22yeets22/Adjustable-Power-Supply/Wiring Diagram.kicad_sch

## KiCad design Wiring Diagram.kicad_sch (2026-02-19)

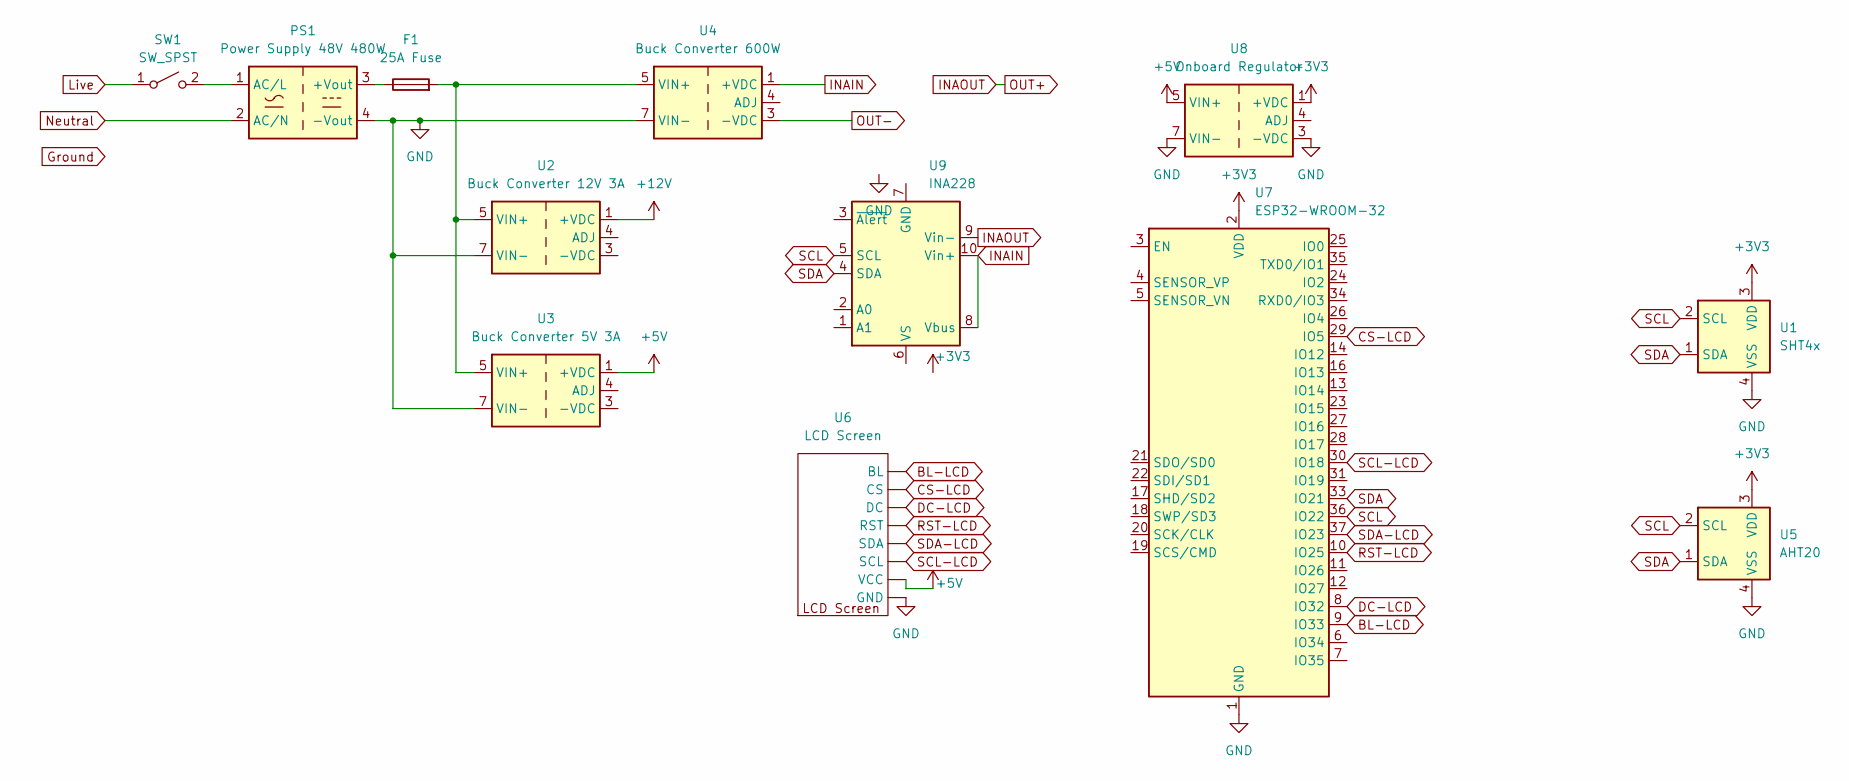
[picture p10: schematic Wiring Diagram.kicad_sch]

Parts:
F1: 25A Fuse
PS1: Power Supply 48V 480W; Converter_ACDC_MeanWell_IRM-60-xx_THT
SW1: SW_SPST
U1: SHT4x; Sensirion_DFN-4_1.5x1.5mm_P0.8mm_SHT4x_NoCentralPad
U2: Buck Converter 12V 3A; Converter_DCDC_Silvertel_Ag99xxLP_THT
U3: Buck Converter 5V 3A; Converter_DCDC_Silvertel_Ag99xxLP_THT
U4: Buck Converter 600W; Converter_DCDC_Silvertel_Ag99xxLP_THT
U5: AHT20; Sensirion_DFN-4_1.5x1.5mm_P0.8mm_SHT4x_NoCentralPad
U6: LCD Screen
U7: ESP32-WROOM-32
U8: Onboard Regulator; Converter_DCDC_Silvertel_Ag99xxLP_THT
U9: INA228; VSSOP-10_3x3mm_P0.5mm

Connections:
+3V3: U1.3 (VDD), U5.3 (VDD), U7.2 (VDD), U8.1 (+VDC), U8.2 (+VDC)
+5V: U3.1 (+VDC), U3.2 (+VDC), U6., U8.5 (VIN+), U8.6 (VIN+)
+12V: U2.1 (+VDC), U2.2 (+VDC)
BL-LCD: U6., U7.9 (IO33)
CS-LCD: U6., U7.29 (IO5)
DC-LCD: U6., U7.8 (IO32)
GND: PS1.4 (-Vout), U1.4 (VSS), U2.7 (VIN-), U2.8 (VIN-), U3.7 (VIN-), U3.8 (VIN-), U4.7 (VIN-), U4.8 (VIN-), U5.4 (VSS), U6., U7.1 (GND), U7.15 (GND), U7.38 (GND), U7.39 (GND), U8.3 (-VDC), U8.7 (VIN-), U8.8 (VIN-)
INAIN: U4.1 (+VDC), U4.2 (+VDC), U9.8 (Vbus), U9.10 (Vin+)
INAOUT: U9.9 (Vin-)
Live: SW1.1 (A)
unnamed: F1.1, PS1.3 (+Vout)
unnamed: F1.2, U2.5 (VIN+), U2.6 (VIN+), U3.5 (VIN+), U3.6 (VIN+), U4.5 (VIN+), U4.6 (VIN+)
unnamed: PS1.1 (AC/L), SW1.2 (B)
Neutral: PS1.2 (AC/N)
OUT-: U4.3 (-VDC)
RST-LCD: U6., U7.10 (IO25)
SCL: U1.2 (SCL), U5.2 (SCL), U7.36 (IO22), U9.5 (SCL)
SCL-LCD: U6., U7.30 (IO18)
SDA: U1.1 (SDA), U5.1 (SDA), U7.33 (IO21), U9.4 (SDA)
SDA-LCD: U6., U7.37 (IO23)
